uw-madison-chem-shops/pressure-monitoring-reactor/heating-block/htrblockassem1.pdf

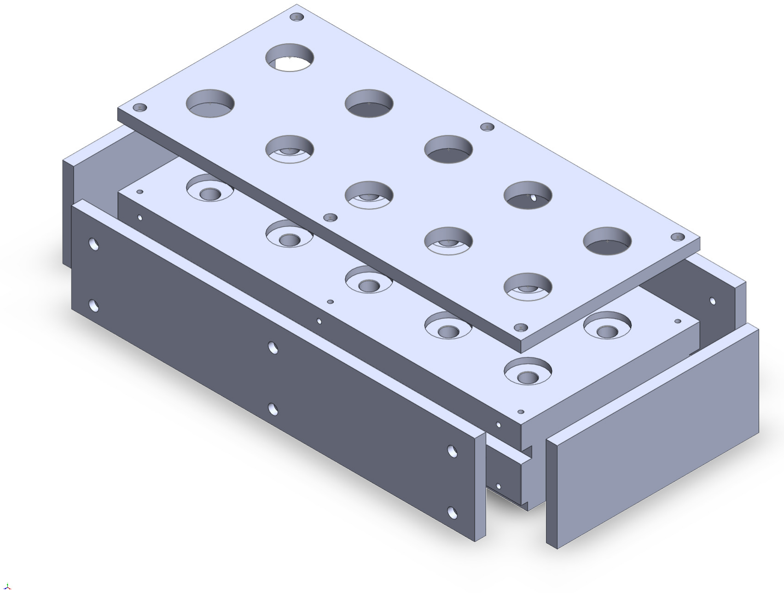
[picture p1: page 1]
