uw-madison-chem-shops/pressure-monitoring-reactor/heating-block/htrblockassem2.pdf

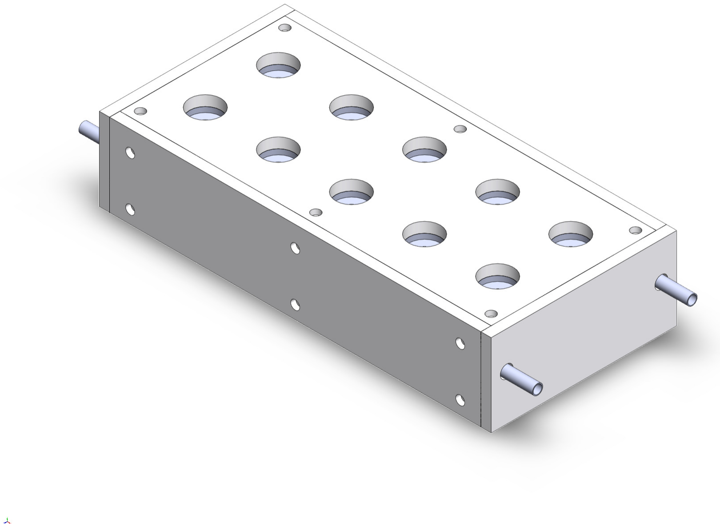
[picture p2: page 1]
