uw-madison-chem-shops/pressure-monitoring-reactor/heating-block/htrblockassem2expl.pdf

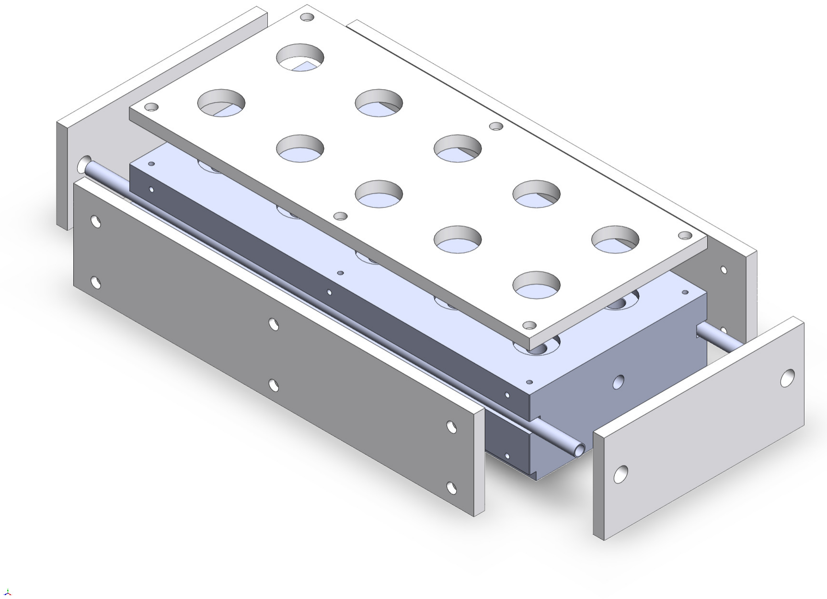
[picture p3: page 1]
