uw-madison-chem-shops/pressure-monitoring-reactor/heating-block/sidebar1 - Sheet1.pdf

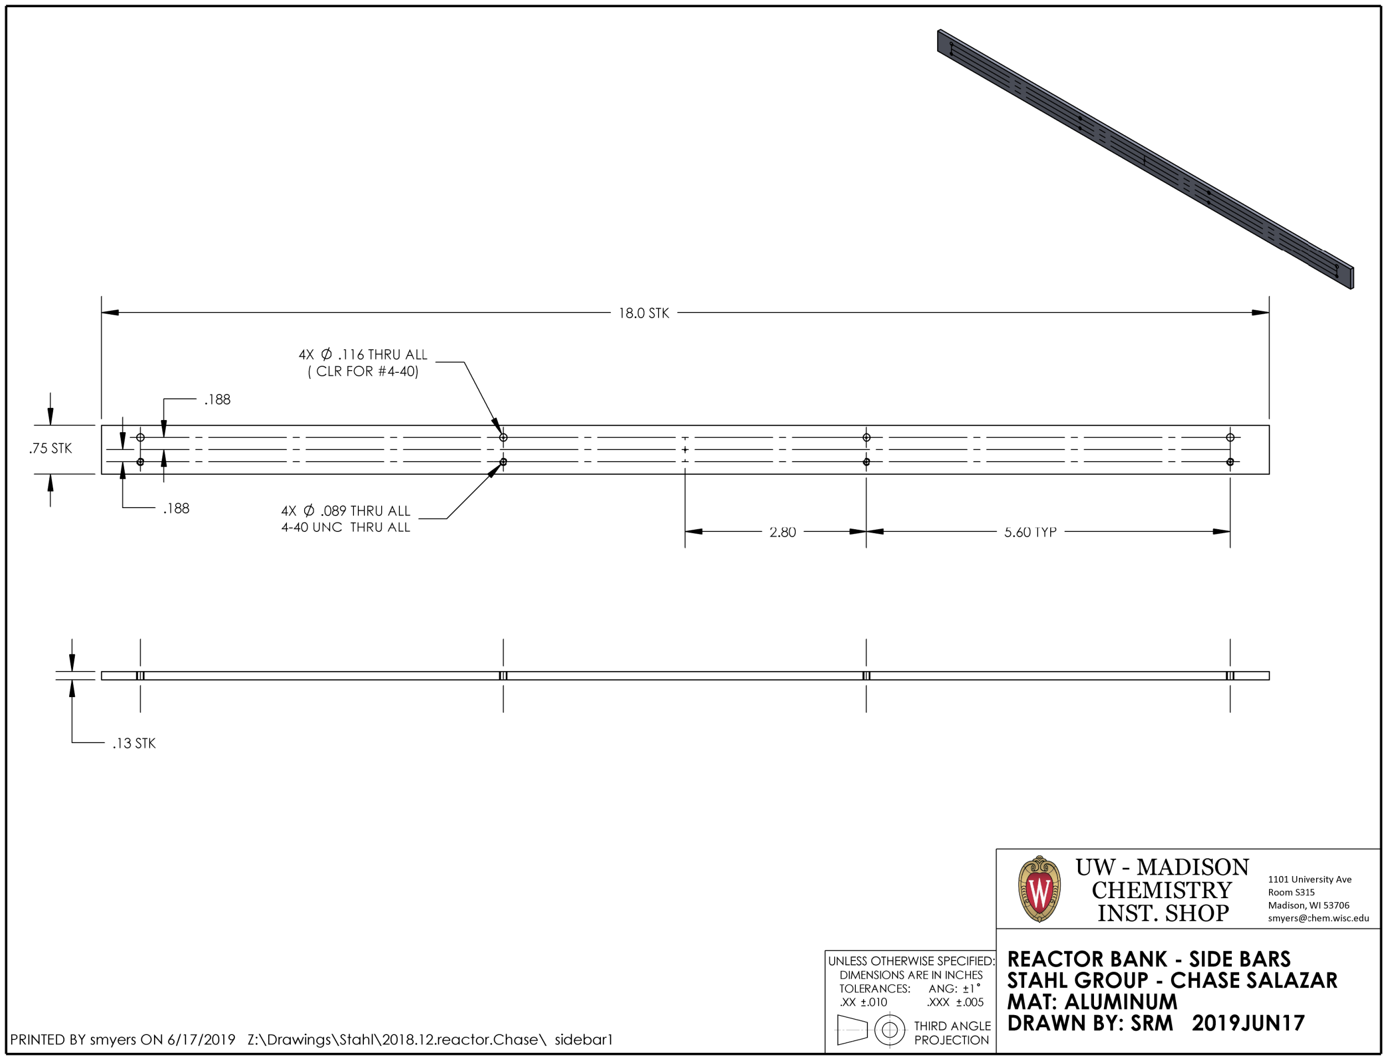
[picture p4: page 1]
