uw-madison-chem-shops/pressure-monitoring-reactor/heating-block/heatblk1 - Sheet1.pdf

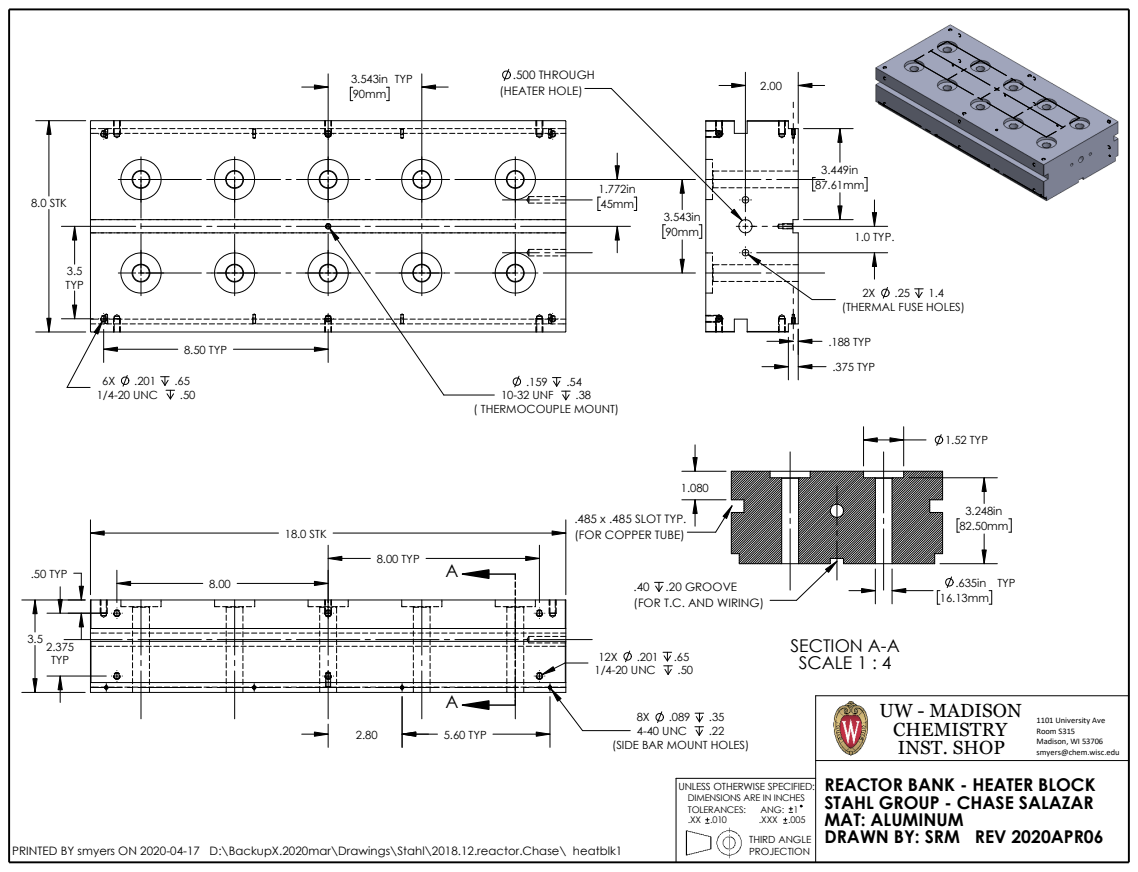
[picture p21: page 1]
.XXX; INST. SHOP; CHEMISTRY; THIRD ANGLE; UW - MADISON; PROJECTION; TOLERANCES:; ANG: 1; 10-32 UNF; ( THERMOCOUPLE MOUNT); 8.50 TYP; 8.0 STK; 3.5 TYP; TYP; 1/4-20 UNC; .50 TYP; 8.00 TYP; 5.60 TYP; 18.0 STK; SECTION A-A SCALE 1 : 4; .20 GROOVE; 1.52 TYP; .635in TYP 16.13mm; .500 THROUGH (HEATER HOLE); 1.0 TYP.; .188 TYP; .375 TYP

(THERMAL FUSE HOLES)

.485 x .485 SLOT TYP.
(FOR COPPER TUBE)

(FOR T.C. AND WIRING)

4-40 UNC
(SIDE BAR MOUNT HOLES)

1101 University Ave
Room S315
Madison, WI 53706
smyers@chem.wisc.edu

UNLESS OTHERWISE SPECIFIED:
DIMENSIONS ARE IN INCHES

REACTOR BANK - HEATER BLOCK
STAHL GROUP - CHASE SALAZAR
MAT: ALUMINUM
DRAWN BY: SRM REV 2020APR06

PRINTED BY smyers ON 2020-04-17 D:\BackupX.2020mar\Drawings\Stahl\2018.12.reactor.Chase\ heatblk1
