uw-madison-chem-shops/pressure-monitoring-reactor/heating-block/heatblk1A - Sheet1.pdf

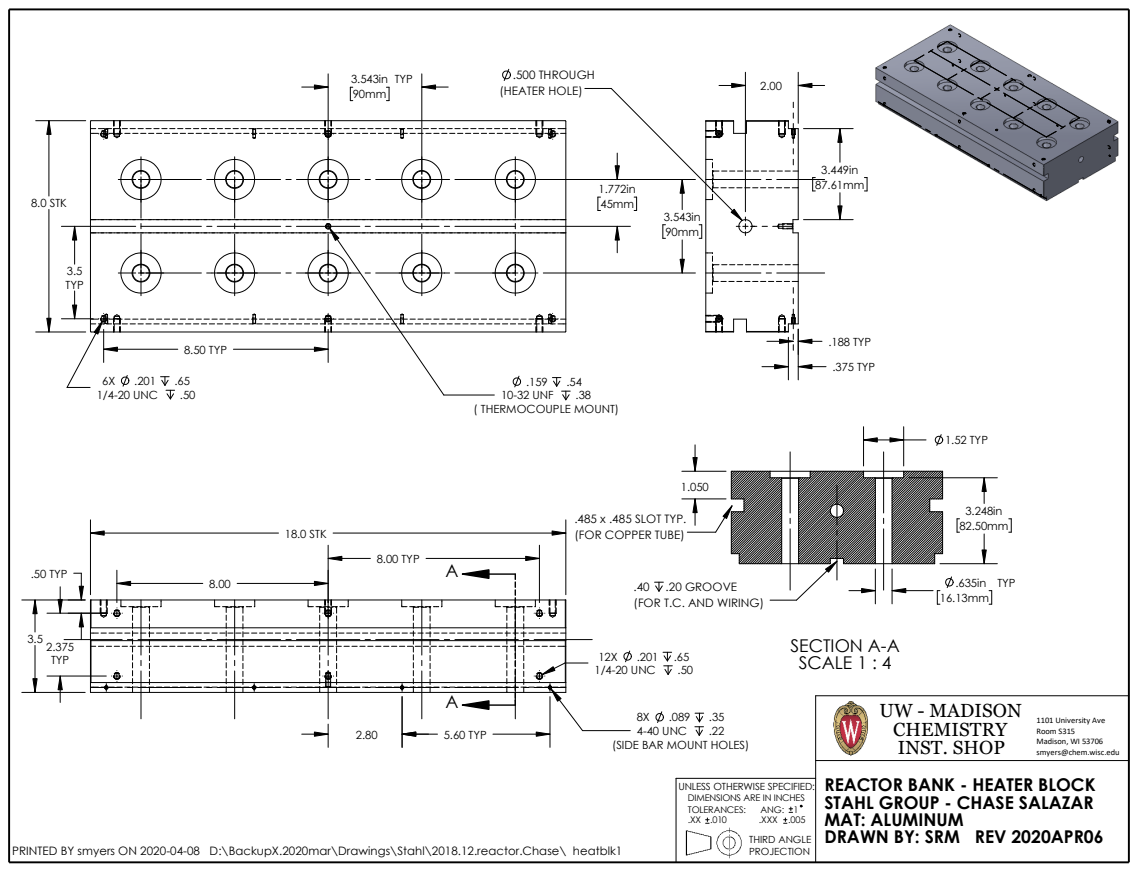
[picture p22: page 1]
UW - MADISON; 1101 University Ave Room S315; .XXX .005; CHEMISTRY; PROJECTION; THIRD ANGLE; TOLERANCES:; ANG: 1; TYP; 8.0 STK; 8.50 TYP; ( THERMOCOUPLE MOUNT); 10-32 UNF; 1/4-20 UNC; .500 THROUGH (HEATER HOLE); .375 TYP; .188 TYP; 5.60 TYP; 18.0 STK; 8.00 TYP; 4-40 UNC 2.80; .50 TYP; SECTION A-A SCALE 1 : 4; 1.52 TYP; .20 GROOVE

.485 x .485 SLOT TYP.
(FOR COPPER TUBE)

(FOR T.C. AND WIRING)

(SIDE BAR MOUNT HOLES)

Madison, WI 53706 INST. SHOP

smyers@chem.wisc.edu

UNLESS OTHERWISE SPECIFIED:
DIMENSIONS ARE IN INCHES

REACTOR BANK - HEATER BLOCK
STAHL GROUP - CHASE SALAZAR
MAT: ALUMINUM
DRAWN BY: SRM REV 2020APR06

PRINTED BY smyers ON 2020-04-08 D:\BackupX.2020mar\Drawings\Stahl\2018.12.reactor.Chase\ heatblk1
