uw-madison-chem-shops/pressure-monitoring-reactor/reactor-cell/Assem1 - Sheet1.pdf

B

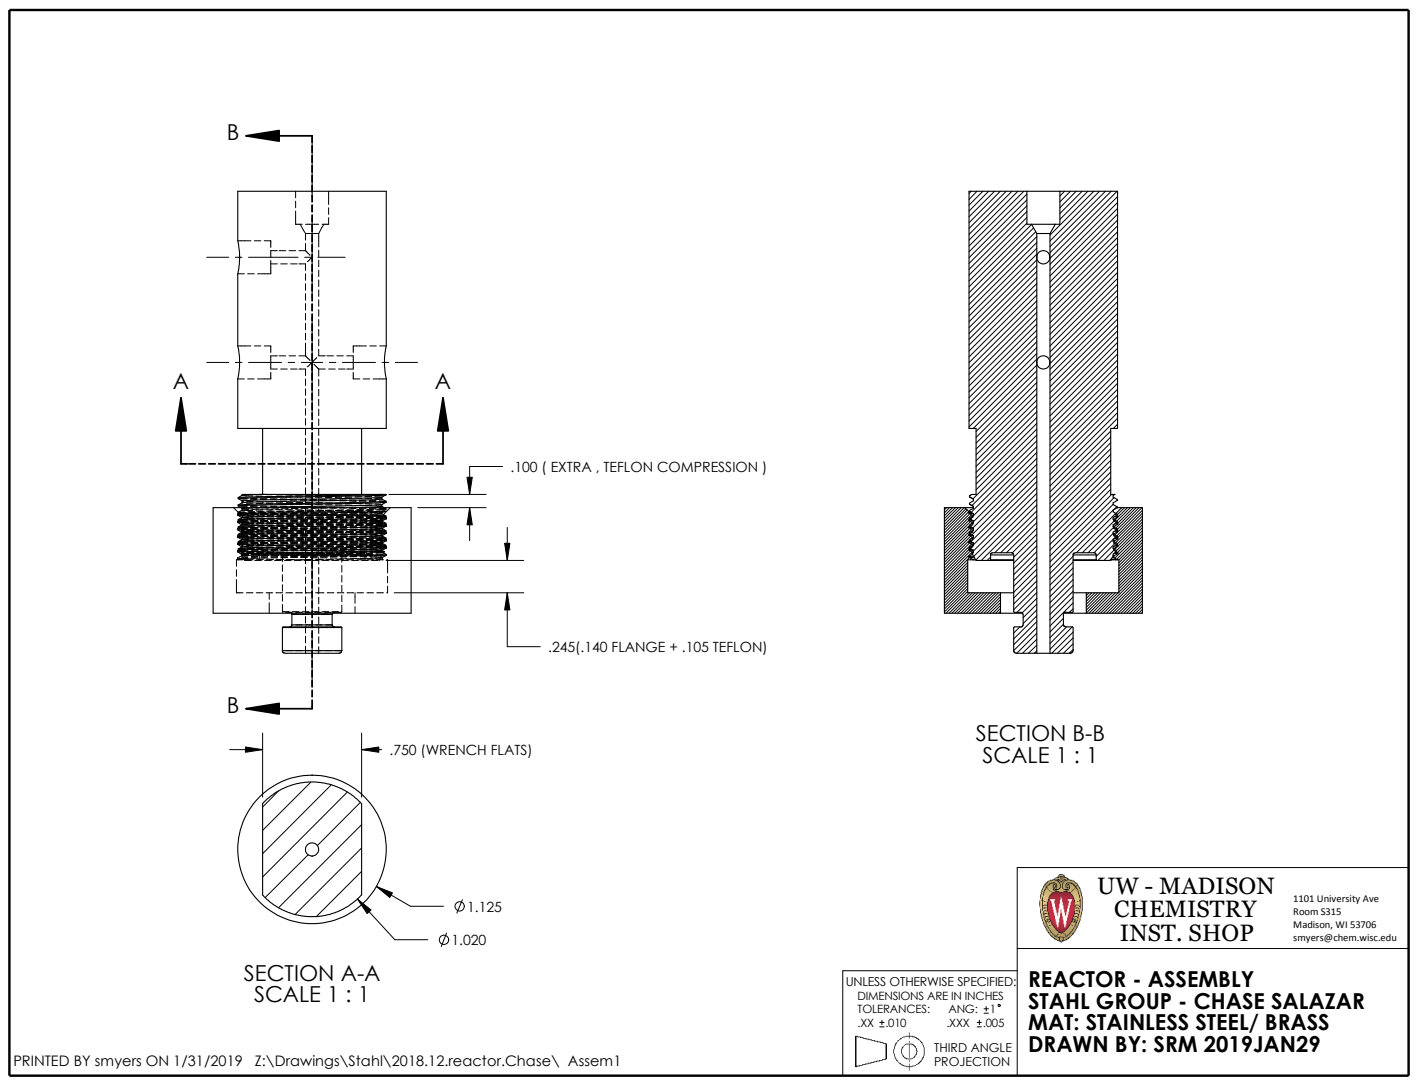
[picture p23: page 1]
.245(.140 FLANGE + .105 TEFLON); PROJECTION; .XXX; THIRD ANGLE; CHEMISTRY INST. SHOP; UW - MADISON; TOLERANCES:; ANG: 1; SECTION B-B SCALE 1 : 1; SECTION A-A SCALE 1 : 1; .750 (WRENCH FLATS)

.100 ( EXTRA , TEFLON COMPRESSION )

1101 University Ave
Room S315
Madison, WI 53706
smyers@chem.wisc.edu

UNLESS OTHERWISE SPECIFIED:
DIMENSIONS ARE IN INCHES

REACTOR - ASSEMBLY
STAHL GROUP - CHASE SALAZAR
MAT: STAINLESS STEEL/ BRASS
DRAWN BY: SRM 2019JAN29

PRINTED BY smyers ON 1/31/2019 Z:\Drawings\Stahl\2018.12.reactor.Chase\ Assem1
