uw-madison-chem-shops/pressure-monitoring-reactor/reactor-cell/body1 - Sheet1.pdf

A

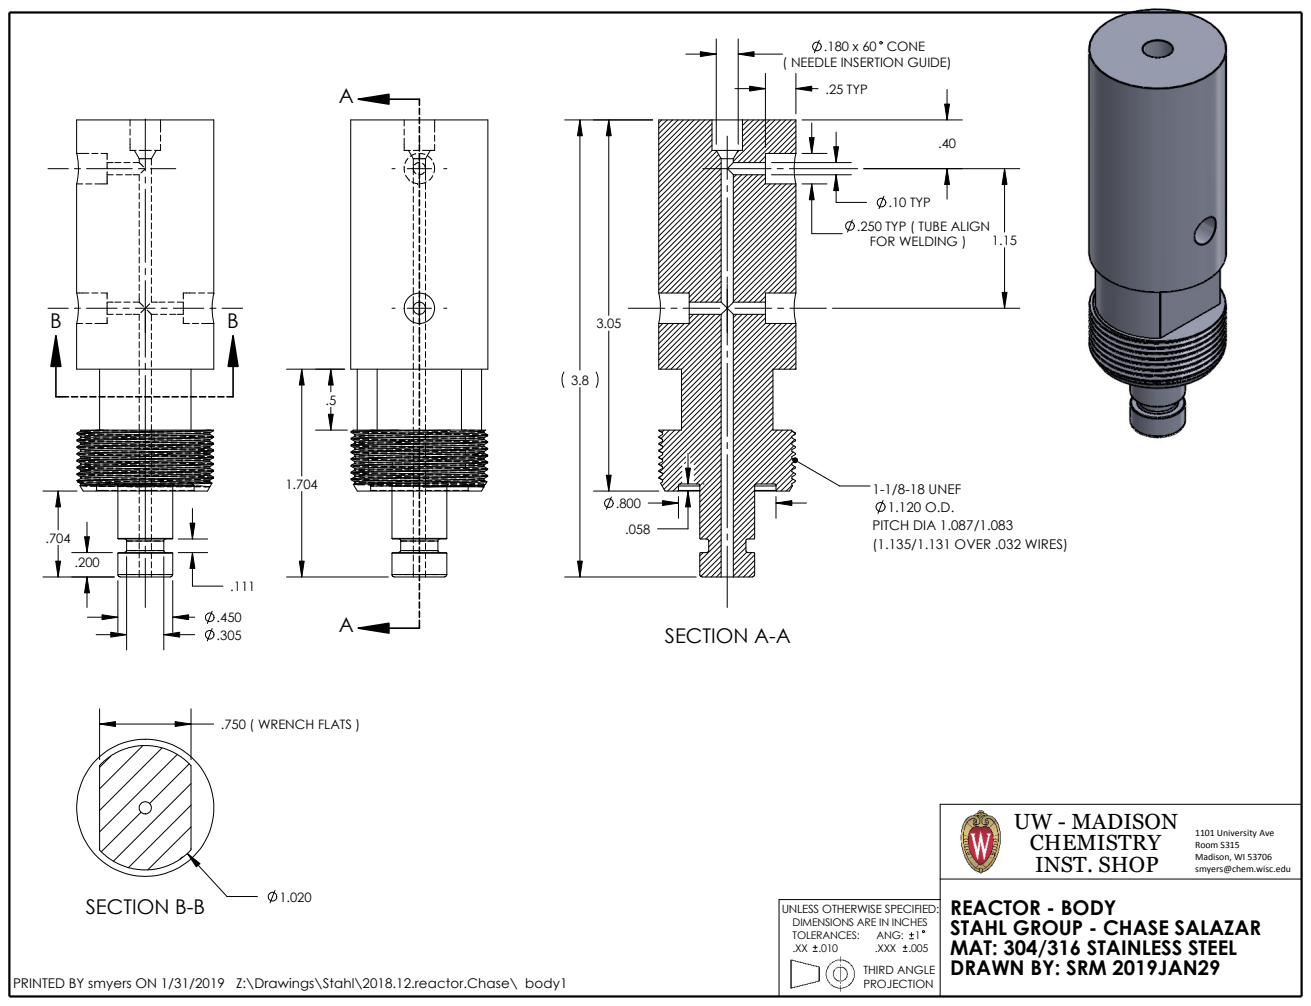
[picture p24: page 1]
A SECTION A-A; 1-1/8-18 UNEF 1.120 O.D. PITCH DIA 1.087/1.083 (1.135/1.131 OVER .032 WIRES); .25 TYP; CONE; SECTION B-B; .750 ( WRENCH FLATS ); .XXX; INST. SHOP; CHEMISTRY; THIRD ANGLE; UW - MADISON; PROJECTION; TOLERANCES:; ANG: 1

( NEEDLE INSERTION GUIDE)

.10 TYP
.250 TYP ( TUBE ALIGN
FOR WELDING )

1101 University Ave
Room S315
Madison, WI 53706
smyers@chem.wisc.edu

UNLESS OTHERWISE SPECIFIED:
DIMENSIONS ARE IN INCHES

REACTOR - BODY
STAHL GROUP - CHASE SALAZAR
MAT: 304/316 STAINLESS STEEL
DRAWN BY: SRM 2019JAN29

PRINTED BY smyers ON 1/31/2019 Z:\Drawings\Stahl\2018.12.reactor.Chase\ body1
