uw-madison-chem-shops/pressure-monitoring-reactor/reactor-cell/body1a - Sheet1.pdf

A

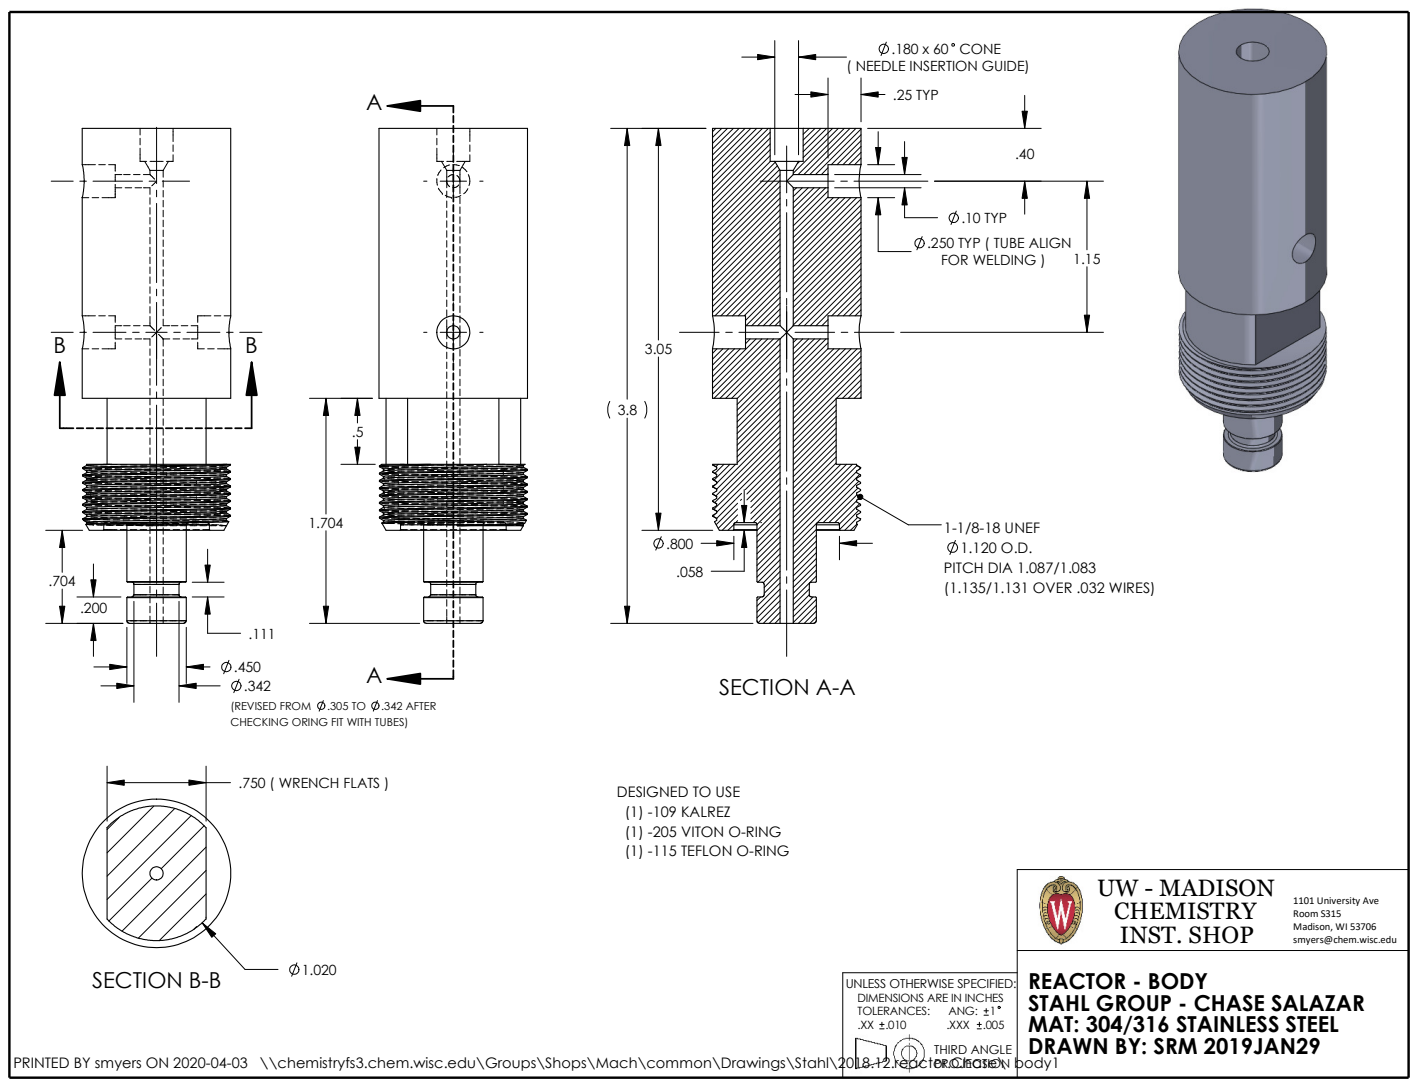
[picture p25: page 1]
Madison, WI 53706; PROJECTION; 1101 University Ave; CHEMISTRY; THIRD ANGLE; INST. SHOP; smyers@chem.wisc.edu; UW - MADISON; Room S315; .XXX .005; TOLERANCES:; ANG: 1; (REVISED FROM; .342 AFTER; A SECTION A-A; 1-1/8-18 UNEF 1.120 O.D. PITCH DIA 1.087/1.083 (1.135/1.131 OVER .032 WIRES); .180 x 60 CONE; .25 TYP; SECTION B-B; .750 ( WRENCH FLATS )

( NEEDLE INSERTION GUIDE)

.10 TYP
.250 TYP ( TUBE ALIGN
FOR WELDING )

CHECKING ORING FIT WITH TUBES)

DESIGNED TO USE
(1) -109 KALREZ
(1) -205 VITON O-RING
(1) -115 TEFLON O-RING

UNLESS OTHERWISE SPECIFIED:
DIMENSIONS ARE IN INCHES

REACTOR - BODY
STAHL GROUP - CHASE SALAZAR
MAT: 304/316 STAINLESS STEEL
DRAWN BY: SRM 2019JAN29

PRINTED BY smyers ON 2020-04-03 \\chemistryfs3.chem.wisc.edu\Groups\Shops\Mach\common\Drawings\Stahl\2018.12.reactor.Chase\ body1
