uw-madison-chem-shops/pressure-monitoring-reactor/reactor-cell/clampring1 - Sheet1.pdf

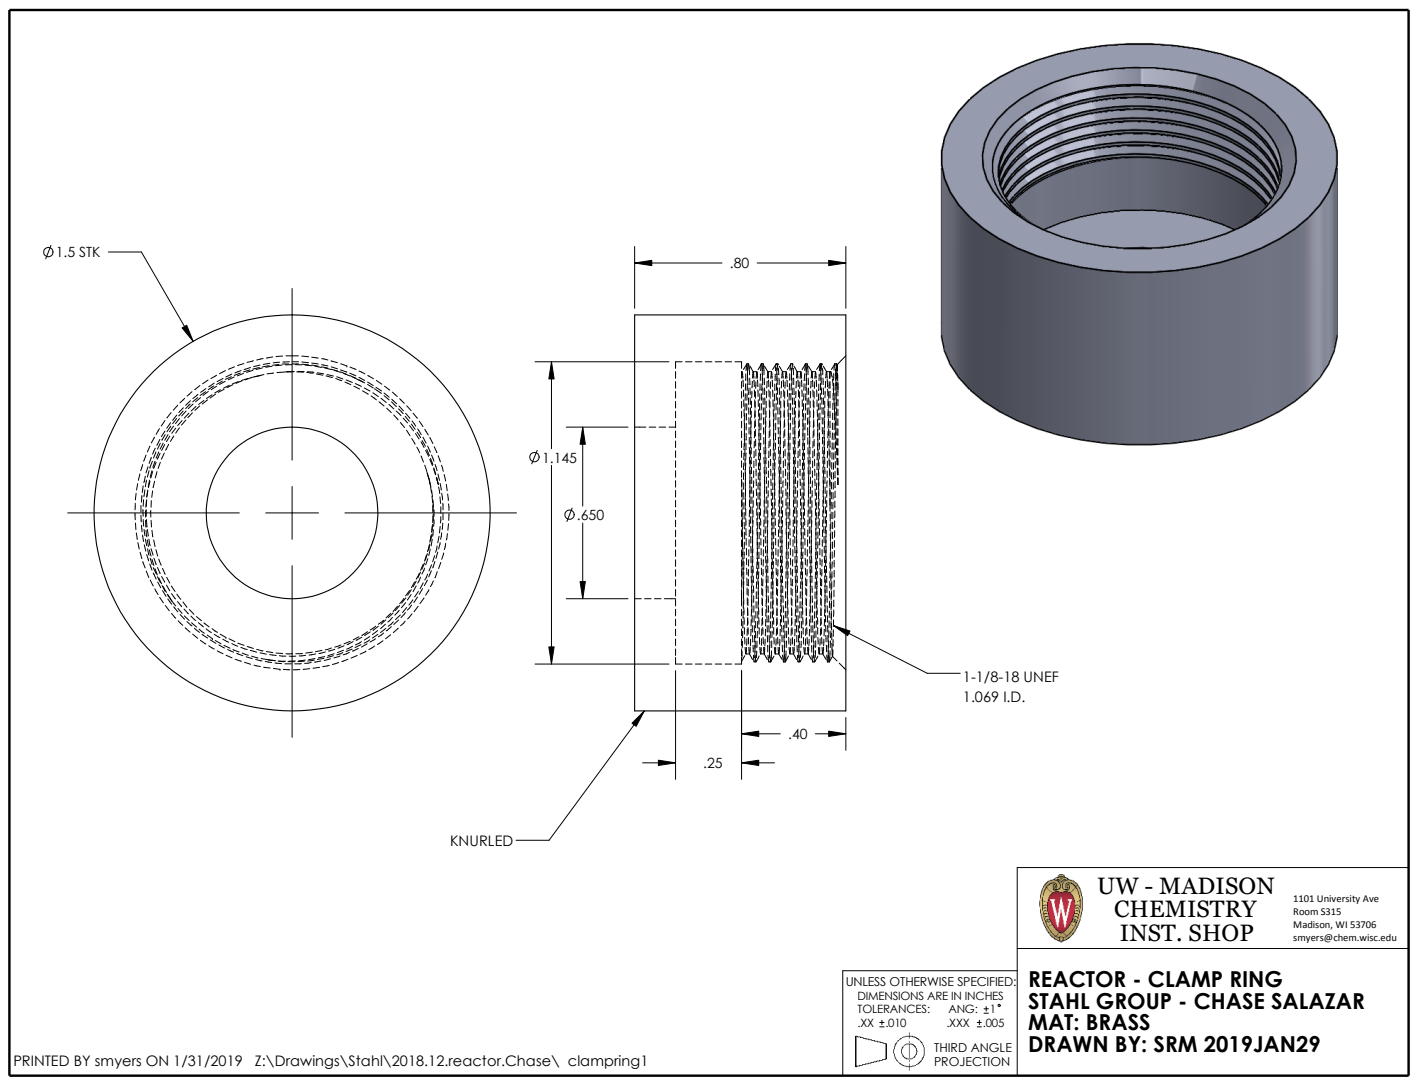
[picture p26: page 1]
1-1/8-18 UNEF; KNURLED; 1.5 STK; INST. SHOP; 1101 University Ave CHEMISTRY; Room S315; UW - MADISON; .XXX; THIRD ANGLE PROJECTION; TOLERANCES:; ANG: 1

Madison, WI 53706
smyers@chem.wisc.edu

UNLESS OTHERWISE SPECIFIED:
DIMENSIONS ARE IN INCHES

REACTOR - CLAMP RING
STAHL GROUP - CHASE SALAZAR
MAT: BRASS
DRAWN BY: SRM 2019JAN29

PRINTED BY smyers ON 1/31/2019 Z:\Drawings\Stahl\2018.12.reactor.Chase\ clampring1
