uw-madison-chem-shops/pressure-monitoring-reactor/reactor-cell/reactortubes1 - Sheet1.pdf

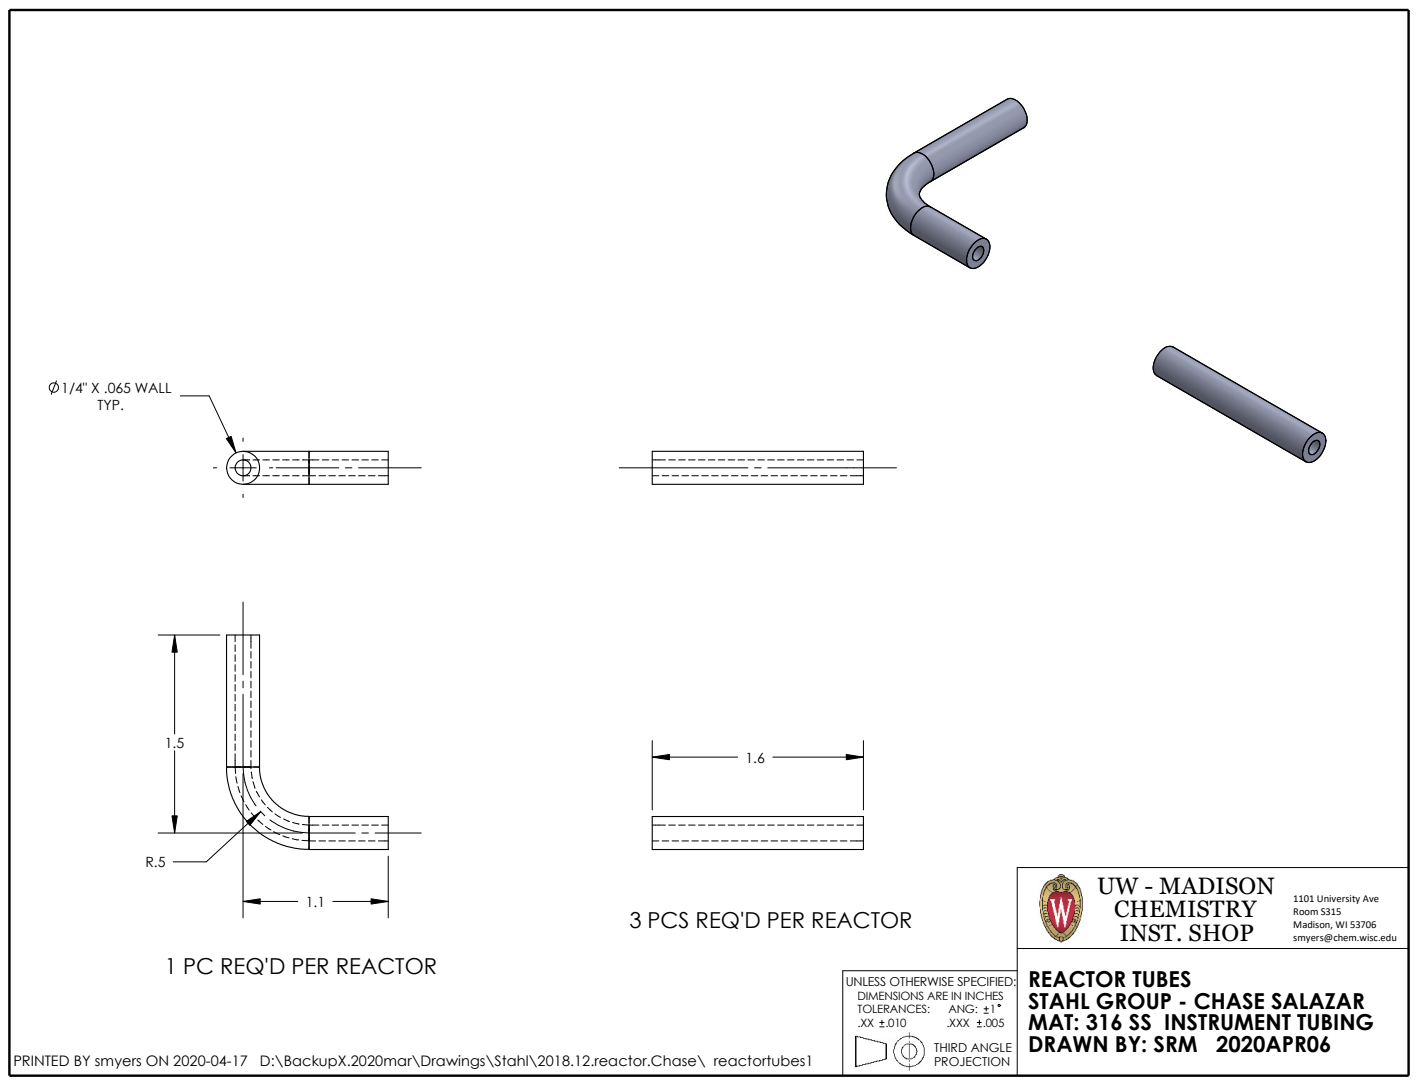
[picture p27: page 1]
Madison, WI 53706; PROJECTION; 1101 University Ave; CHEMISTRY; THIRD ANGLE; INST. SHOP; smyers@chem.wisc.edu; UW - MADISON; Room S315; .XXX .005; TOLERANCES:; ANG: 1; 1/4" X .065 WALL TYP.

3 PCS REQ'D PER REACTOR

1 PC REQ'D PER REACTOR

UNLESS OTHERWISE SPECIFIED:
DIMENSIONS ARE IN INCHES

REACTOR TUBES
STAHL GROUP - CHASE SALAZAR
MAT: 316 SS INSTRUMENT TUBING
DRAWN BY: SRM 2020APR06

PRINTED BY smyers ON 2020-04-17 D:\BackupX.2020mar\Drawings\Stahl\2018.12.reactor.Chase\ reactortubes1
